benninge/wearable_suit/arduino/src/rs485_slave/rs485_slave.ino

#include "RS485_protocol.h"

const byte ENABLE_PIN = 7;
const byte SLAVE_ID = 1;

  void fWrite (const byte content)
    {
    Serial.write (content);
    }

  int fAvailable ()
    {
    return Serial.available ();
    }

  int fRead ()
    {
    return Serial.read ();
    }
void setup()
{
  Serial.begin (28800);
  pinMode (ENABLE_PIN, OUTPUT);  // driver output enable
  digitalWrite (ENABLE_PIN, LOW);
}

void loop()
{
  byte buffer [10];

  //byte received = recvMsg (fAvailable, fRead, buffer, sizeof (buffer));

  if (true)
    {
    //if (buffer [0] != SLAVE_ID)
    //  return;  // not my device

    //if (buffer [1] != 2)
    //  return;  // unknown command

    byte msg [] = {
       0,  // device 0 (master)
       3,  // turn light on command received
    };

    delay (2);  // give the master a moment to prepare to receive
    digitalWrite (ENABLE_PIN, HIGH);  // enable sending
    sendMsg (fWrite, msg, sizeof msg);
    Serial.flush();
    digitalWrite (ENABLE_PIN, LOW);  // disable sending
    delay (1000);
   }

}
